bigtreetech/HermitCrab/HermitCrab2/BIGTREETECH Hermit Crab 2 CAN-Overlay.pdf

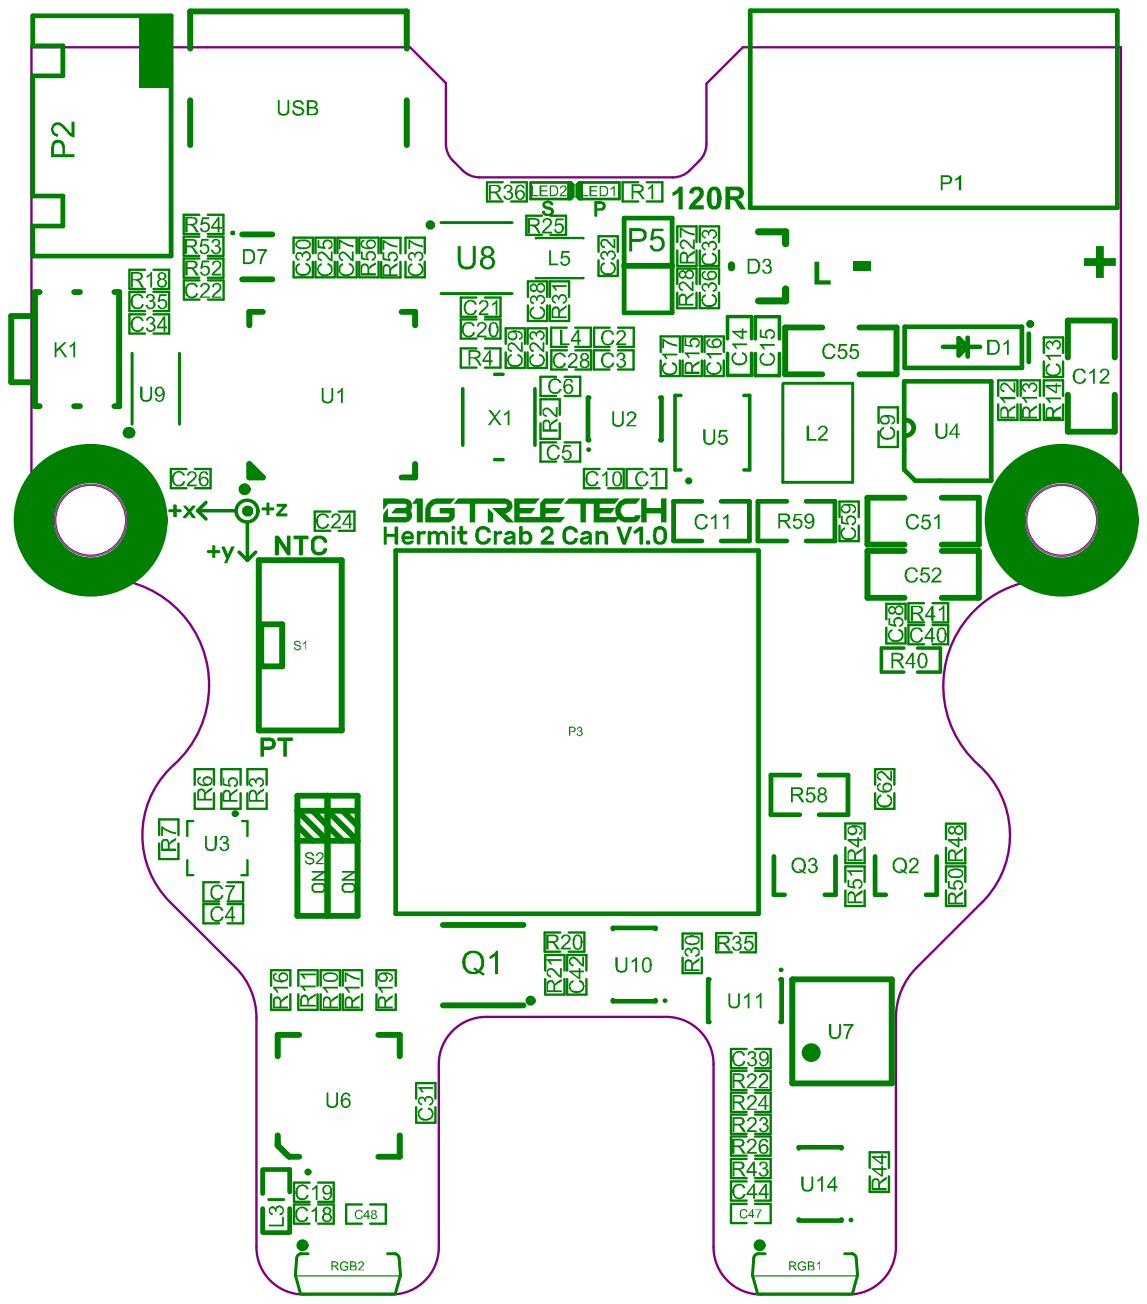
[picture p43: page 1]

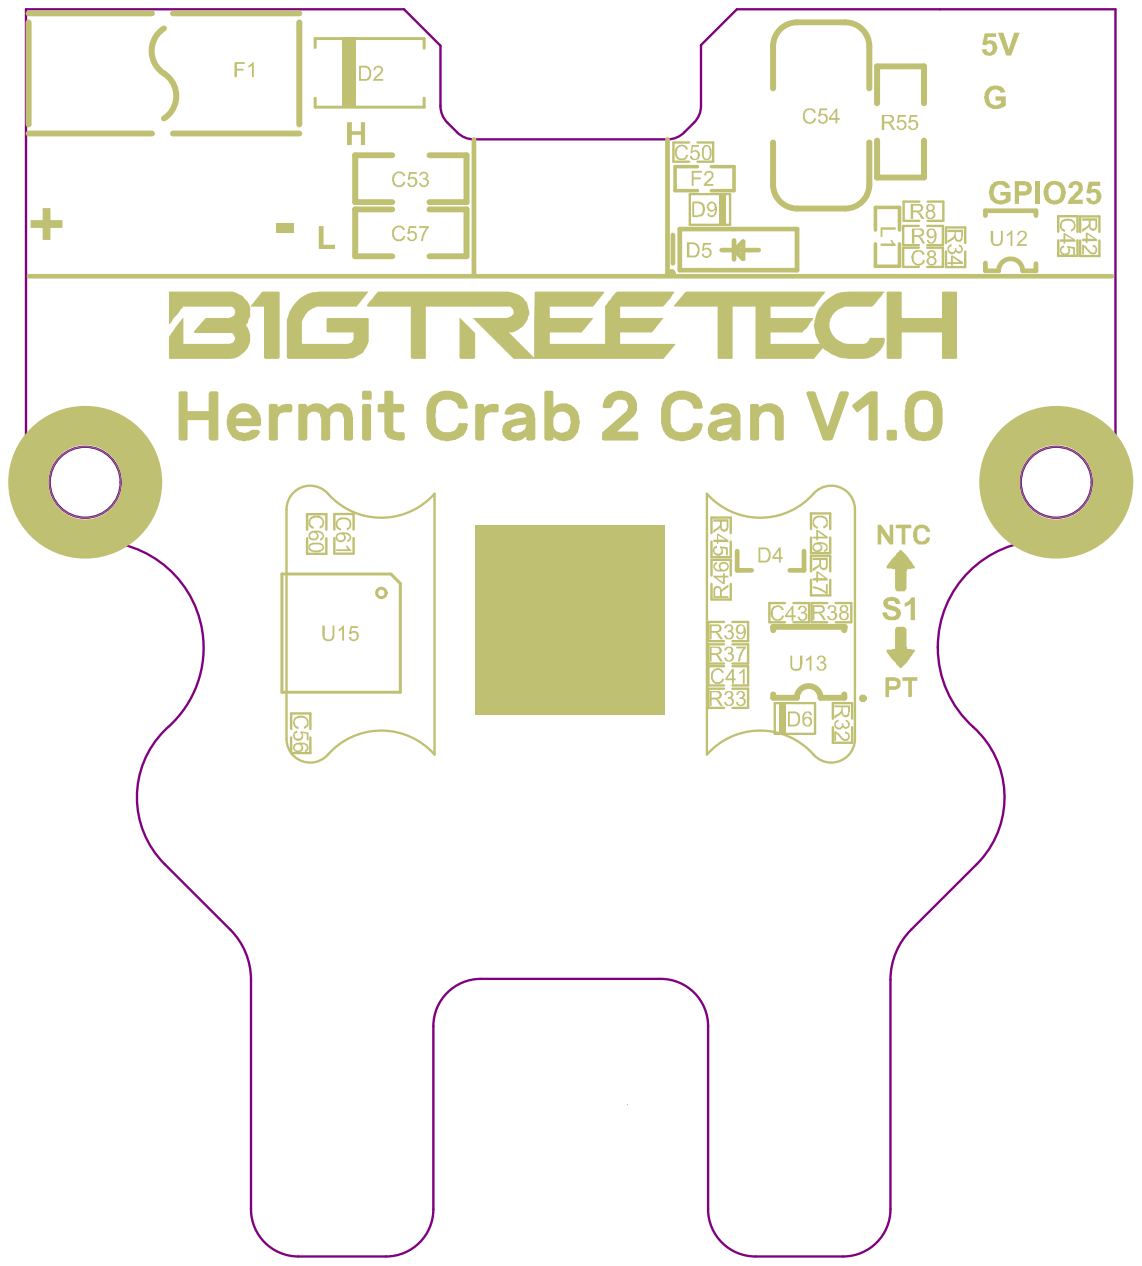
[picture p44: page 2]
