bigtreetech/HermitCrab/HermitCrab1/HERMIT CRAB.pdf

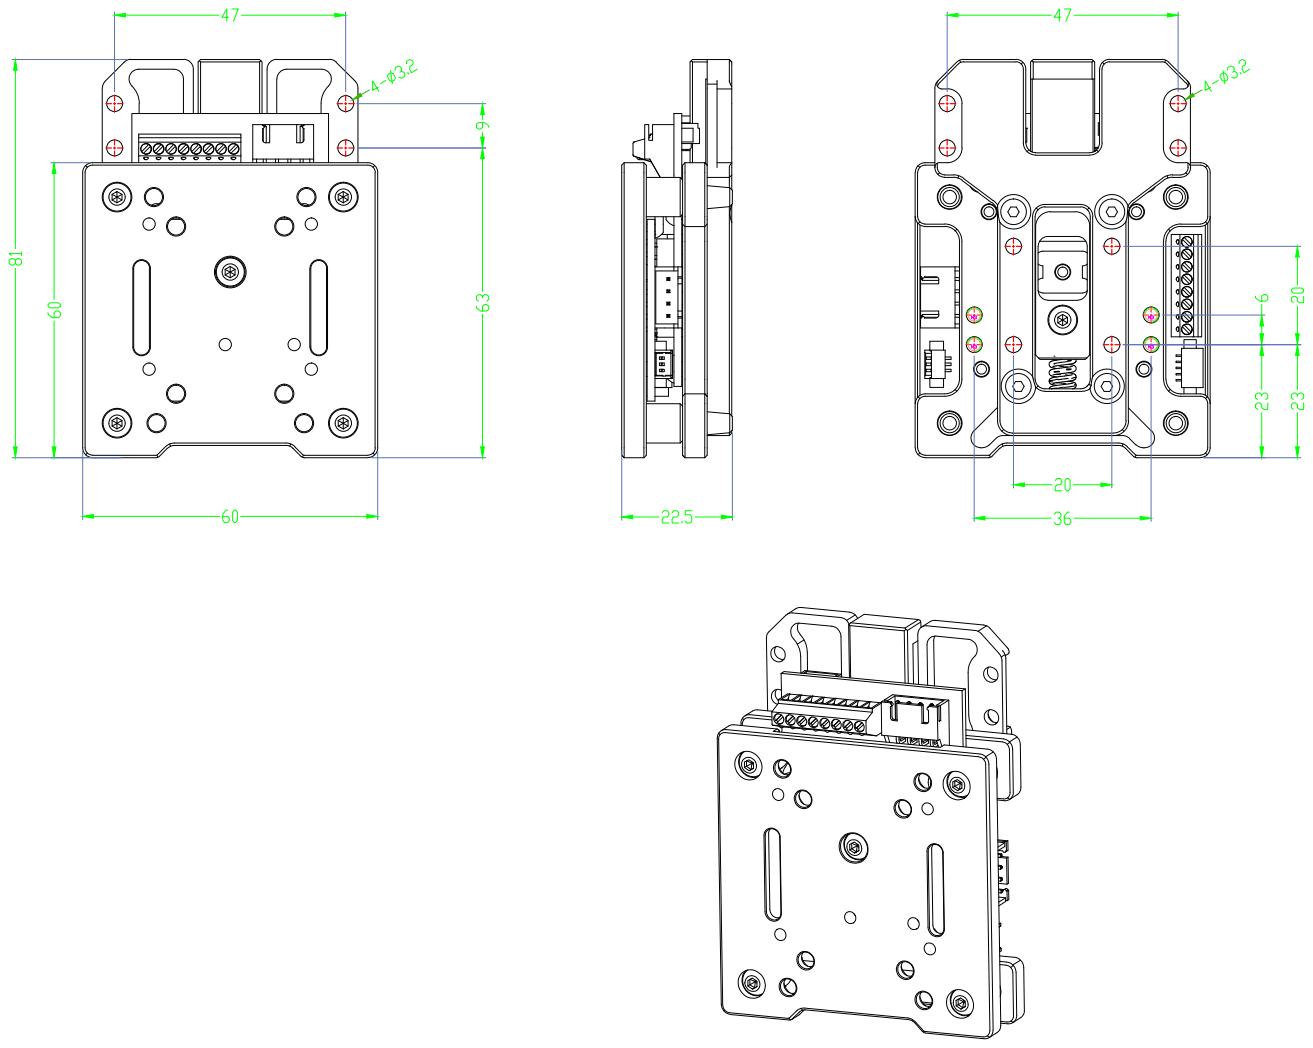
[picture p45: page 1]
